experientials/bob-929/Face/929 bob front.png

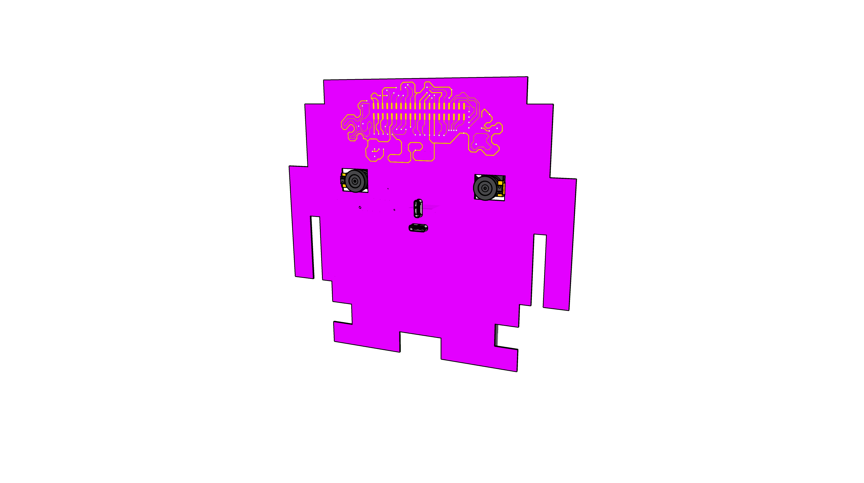
Face/929 bob front.png
