experientials/bob-929/Face/929-inverted.png

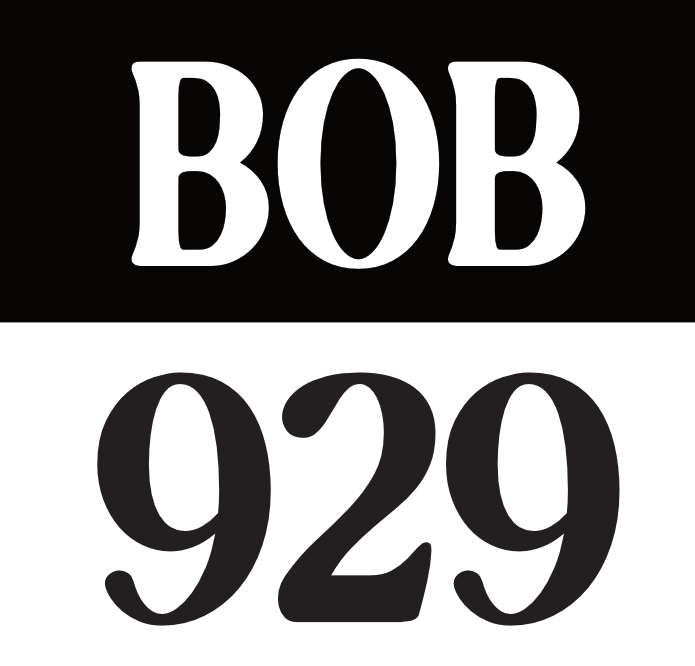
Face/929-inverted.png
