experientials/bob-929/Face/Ziloo face board.jpg

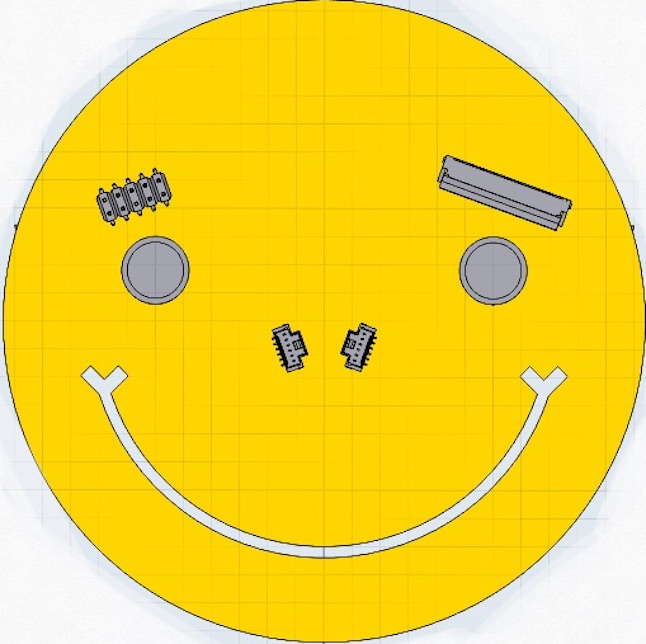
Face/Ziloo face board.jpg
